clm302002/lily58custom/pictures/adafruit PCB Back.jpg

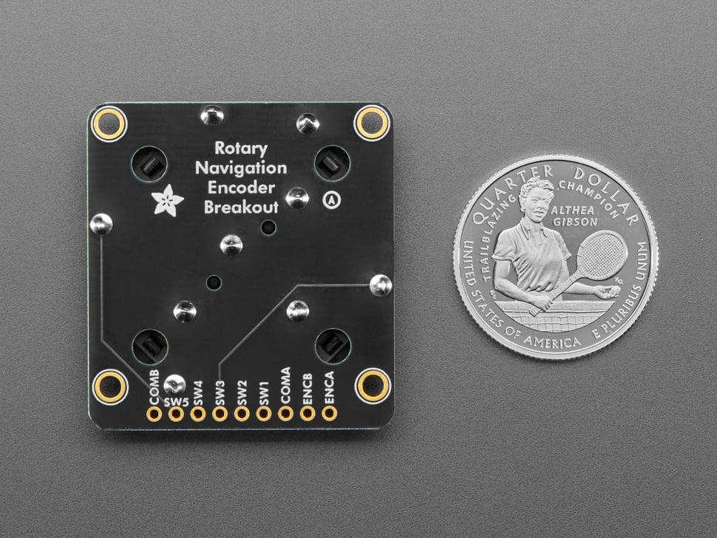
pictures/adafruit PCB Back.jpg
