clm302002/lily58custom/pictures/adafruit PCB Front.png

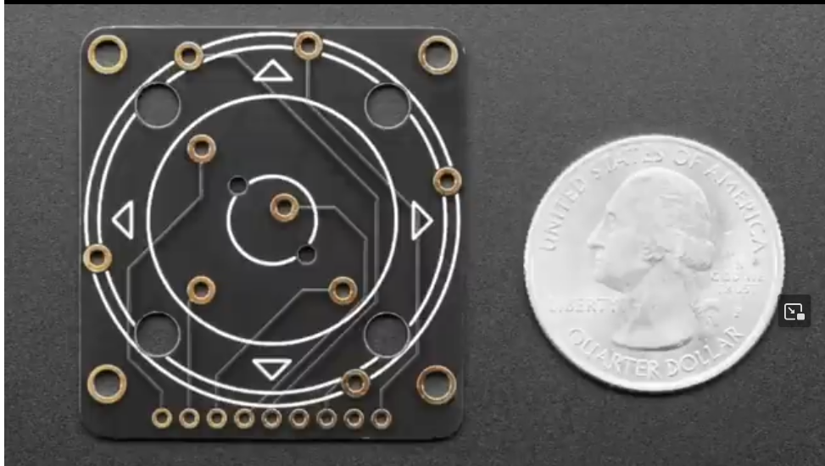
pictures/adafruit PCB Front.png
