clm302002/lily58custom/pictures/ANO Directional Navigation and Scroll Wheel Rotary Encoder 2.jpg

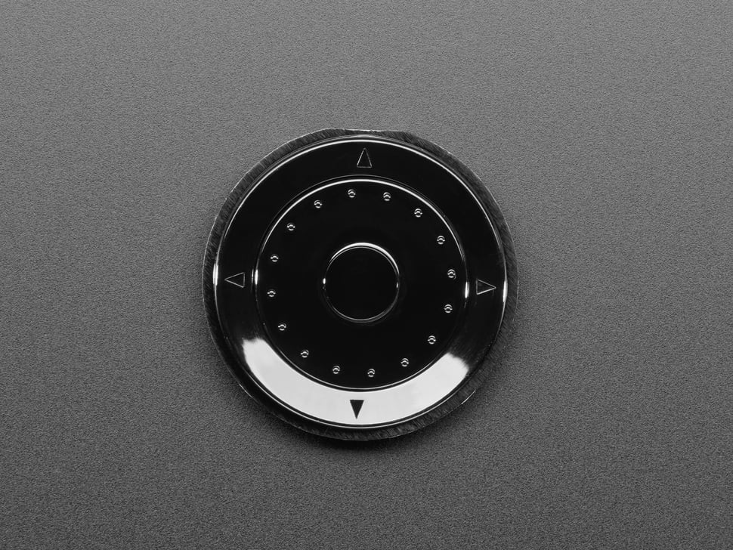
pictures/ANO Directional Navigation and Scroll Wheel Rotary Encoder 2.jpg
