clm302002/lily58custom/pictures/PXL_20250418_045556435.jpg

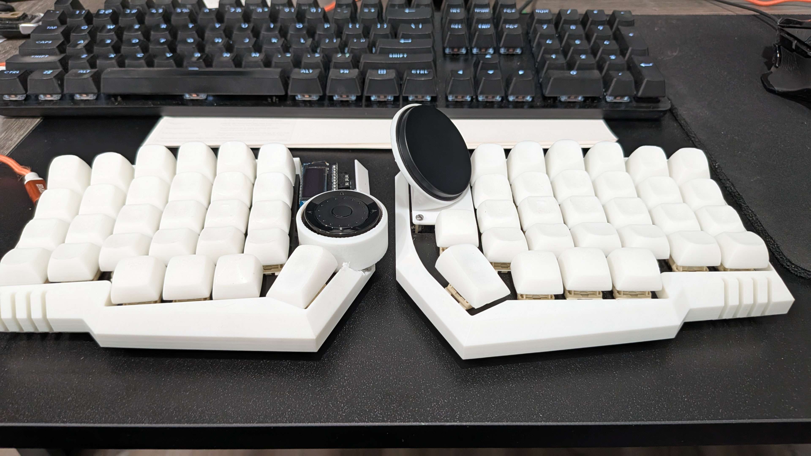
pictures/PXL_20250418_045556435.jpg
